c-malecki/power_supply_v2/Core/Src/adc.c

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
/* Includes ------------------------------------------------------------------*/
#include "adc.h"

ADC_HandleTypeDef hadc1;
ADC_HandleTypeDef hadc2;
ADC_HandleTypeDef hadc5;
DMA_HandleTypeDef hdma_adc1;
DMA_HandleTypeDef hdma_adc2;
DMA_HandleTypeDef hdma_adc5;

/* ADC1 init function */
void MX_ADC1_Init(void)
{

  ADC_MultiModeTypeDef multimode = {0};
  ADC_ChannelConfTypeDef sConfig = {0};

  /** Common config
  */
  hadc1.Instance = ADC1;
  hadc1.Init.ClockPrescaler = ADC_CLOCK_SYNC_PCLK_DIV4;
  hadc1.Init.Resolution = ADC_RESOLUTION_12B;
  hadc1.Init.DataAlign = ADC_DATAALIGN_RIGHT;
  hadc1.Init.GainCompensation = 0;
  hadc1.Init.ScanConvMode = ADC_SCAN_DISABLE;
  hadc1.Init.EOCSelection = ADC_EOC_SINGLE_CONV;
  hadc1.Init.LowPowerAutoWait = DISABLE;
  hadc1.Init.ContinuousConvMode = DISABLE;
  hadc1.Init.NbrOfConversion = 1;
  hadc1.Init.DiscontinuousConvMode = DISABLE;
  hadc1.Init.ExternalTrigConv = ADC_SOFTWARE_START;
  hadc1.Init.ExternalTrigConvEdge = ADC_EXTERNALTRIGCONVEDGE_NONE;
  hadc1.Init.DMAContinuousRequests = DISABLE;
  hadc1.Init.Overrun = ADC_OVR_DATA_PRESERVED;
  hadc1.Init.OversamplingMode = ENABLE;
  hadc1.Init.Oversampling.Ratio = ADC_OVERSAMPLING_RATIO_16;
  hadc1.Init.Oversampling.RightBitShift = ADC_RIGHTBITSHIFT_NONE;
  hadc1.Init.Oversampling.TriggeredMode = ADC_TRIGGEREDMODE_SINGLE_TRIGGER;
  hadc1.Init.Oversampling.OversamplingStopReset = ADC_REGOVERSAMPLING_CONTINUED_MODE;
  if (HAL_ADC_Init(&hadc1) != HAL_OK)
  {
    Error_Handler();
  }

  /** Configure the ADC multi-mode
  */
  multimode.Mode = ADC_MODE_INDEPENDENT;
  if (HAL_ADCEx_MultiModeConfigChannel(&hadc1, &multimode) != HAL_OK)
  {
    Error_Handler();
  }

  /** Configure Regular Channel
  */
  sConfig.Channel = ADC_CHANNEL_11;
  sConfig.Rank = ADC_REGULAR_RANK_1;
  sConfig.SamplingTime = ADC_SAMPLETIME_2CYCLES_5;
  sConfig.SingleDiff = ADC_SINGLE_ENDED;
  sConfig.OffsetNumber = ADC_OFFSET_NONE;
  sConfig.Offset = 0;
  if (HAL_ADC_ConfigChannel(&hadc1, &sConfig) != HAL_OK)
  {
    Error_Handler();
  }
}
/* ADC2 init function */
void MX_ADC2_Init(void)
{

  ADC_ChannelConfTypeDef sConfig = {0};

  /** Common config
  */
  hadc2.Instance = ADC2;
  hadc2.Init.ClockPrescaler = ADC_CLOCK_SYNC_PCLK_DIV4;
  hadc2.Init.Resolution = ADC_RESOLUTION_12B;
  hadc2.Init.DataAlign = ADC_DATAALIGN_RIGHT;
  hadc2.Init.GainCompensation = 0;
  hadc2.Init.ScanConvMode = ADC_SCAN_DISABLE;
  hadc2.Init.EOCSelection = ADC_EOC_SINGLE_CONV;
  hadc2.Init.LowPowerAutoWait = DISABLE;
  hadc2.Init.ContinuousConvMode = DISABLE;
  hadc2.Init.NbrOfConversion = 1;
  hadc2.Init.DiscontinuousConvMode = DISABLE;
  hadc2.Init.ExternalTrigConv = ADC_SOFTWARE_START;
  hadc2.Init.ExternalTrigConvEdge = ADC_EXTERNALTRIGCONVEDGE_NONE;
  hadc2.Init.DMAContinuousRequests = DISABLE;
  hadc2.Init.Overrun = ADC_OVR_DATA_PRESERVED;
  hadc2.Init.OversamplingMode = ENABLE;
  hadc2.Init.Oversampling.Ratio = ADC_OVERSAMPLING_RATIO_16;
  hadc2.Init.Oversampling.RightBitShift = ADC_RIGHTBITSHIFT_NONE;
  hadc2.Init.Oversampling.TriggeredMode = ADC_TRIGGEREDMODE_SINGLE_TRIGGER;
  hadc2.Init.Oversampling.OversamplingStopReset = ADC_REGOVERSAMPLING_CONTINUED_MODE;
  if (HAL_ADC_Init(&hadc2) != HAL_OK)
  {
    Error_Handler();
  }

  /** Configure Regular Channel
  */
  sConfig.Channel = ADC_CHANNEL_12;
  sConfig.Rank = ADC_REGULAR_RANK_1;
  sConfig.SamplingTime = ADC_SAMPLETIME_2CYCLES_5;
  sConfig.SingleDiff = ADC_SINGLE_ENDED;
  sConfig.OffsetNumber = ADC_OFFSET_NONE;
  sConfig.Offset = 0;
  if (HAL_ADC_ConfigChannel(&hadc2, &sConfig) != HAL_OK)
  {
    Error_Handler();
  }
}
/* ADC5 init function */
void MX_ADC5_Init(void)
{

  ADC_ChannelConfTypeDef sConfig = {0};

  /** Common config
  */
  hadc5.Instance = ADC5;
  hadc5.Init.ClockPrescaler = ADC_CLOCK_SYNC_PCLK_DIV4;
  hadc5.Init.Resolution = ADC_RESOLUTION_12B;
  hadc5.Init.DataAlign = ADC_DATAALIGN_RIGHT;
  hadc5.Init.GainCompensation = 0;
  hadc5.Init.ScanConvMode = ADC_SCAN_DISABLE;
  hadc5.Init.EOCSelection = ADC_EOC_SINGLE_CONV;
  hadc5.Init.LowPowerAutoWait = DISABLE;
  hadc5.Init.ContinuousConvMode = DISABLE;
  hadc5.Init.NbrOfConversion = 1;
  hadc5.Init.DiscontinuousConvMode = DISABLE;
  hadc5.Init.ExternalTrigConv = ADC_SOFTWARE_START;
  hadc5.Init.ExternalTrigConvEdge = ADC_EXTERNALTRIGCONVEDGE_NONE;
  hadc5.Init.DMAContinuousRequests = DISABLE;
  hadc5.Init.Overrun = ADC_OVR_DATA_PRESERVED;
  hadc5.Init.OversamplingMode = ENABLE;
  hadc5.Init.Oversampling.Ratio = ADC_OVERSAMPLING_RATIO_16;
  hadc5.Init.Oversampling.RightBitShift = ADC_RIGHTBITSHIFT_NONE;
  hadc5.Init.Oversampling.TriggeredMode = ADC_TRIGGEREDMODE_SINGLE_TRIGGER;
  hadc5.Init.Oversampling.OversamplingStopReset = ADC_REGOVERSAMPLING_CONTINUED_MODE;
  if (HAL_ADC_Init(&hadc5) != HAL_OK)
  {
    Error_Handler();
  }

  /** Configure Regular Channel
  */
  sConfig.Channel = ADC_CHANNEL_1;
  sConfig.Rank = ADC_REGULAR_RANK_1;
  sConfig.SamplingTime = ADC_SAMPLETIME_2CYCLES_5;
  sConfig.SingleDiff = ADC_SINGLE_ENDED;
  sConfig.OffsetNumber = ADC_OFFSET_NONE;
  sConfig.Offset = 0;
  if (HAL_ADC_ConfigChannel(&hadc5, &sConfig) != HAL_OK)
  {
    Error_Handler();
  }
}

static uint32_t HAL_RCC_ADC12_CLK_ENABLED=0;

void HAL_ADC_MspInit(ADC_HandleTypeDef* adcHandle)
{

  GPIO_InitTypeDef GPIO_InitStruct = {0};
  RCC_PeriphCLKInitTypeDef PeriphClkInit = {0};
  if(adcHandle->Instance==ADC1)
  {
  /** Initializes the peripherals clocks
  */
    PeriphClkInit.PeriphClockSelection = RCC_PERIPHCLK_ADC12;
    PeriphClkInit.Adc12ClockSelection = RCC_ADC12CLKSOURCE_SYSCLK;
    if (HAL_RCCEx_PeriphCLKConfig(&PeriphClkInit) != HAL_OK)
    {
      Error_Handler();
    }

    /* ADC1 clock enable */
    HAL_RCC_ADC12_CLK_ENABLED++;
    if(HAL_RCC_ADC12_CLK_ENABLED==1){
      __HAL_RCC_ADC12_CLK_ENABLE();
    }

    __HAL_RCC_GPIOB_CLK_ENABLE();
    /**ADC1 GPIO Configuration
    PB11     ------> ADC1_IN14
    PB12     ------> ADC1_IN11
    */
    GPIO_InitStruct.Pin = OPAMP_3V3B_ADC1_IN14_Pin|OPAMP_3V3A_ADC1_IN11_Pin;
    GPIO_InitStruct.Mode = GPIO_MODE_ANALOG;
    GPIO_InitStruct.Pull = GPIO_NOPULL;
    HAL_GPIO_Init(GPIOB, &GPIO_InitStruct);

    /* ADC1 DMA Init */
    /* ADC1 Init */
    hdma_adc1.Instance = DMA1_Channel3;
    hdma_adc1.Init.Request = DMA_REQUEST_ADC1;
    hdma_adc1.Init.Direction = DMA_PERIPH_TO_MEMORY;
    hdma_adc1.Init.PeriphInc = DMA_PINC_DISABLE;
    hdma_adc1.Init.MemInc = DMA_MINC_ENABLE;
    hdma_adc1.Init.PeriphDataAlignment = DMA_PDATAALIGN_HALFWORD;
    hdma_adc1.Init.MemDataAlignment = DMA_MDATAALIGN_HALFWORD;
    hdma_adc1.Init.Mode = DMA_CIRCULAR;
    hdma_adc1.Init.Priority = DMA_PRIORITY_LOW;
    if (HAL_DMA_Init(&hdma_adc1) != HAL_OK)
    {
      Error_Handler();
    }

    __HAL_LINKDMA(adcHandle,DMA_Handle,hdma_adc1);

    /* ADC1 interrupt Init */
    HAL_NVIC_SetPriority(ADC1_2_IRQn, 0, 0);
    HAL_NVIC_EnableIRQ(ADC1_2_IRQn);
  }
  else if(adcHandle->Instance==ADC2)
  {
  /** Initializes the peripherals clocks
  */
    PeriphClkInit.PeriphClockSelection = RCC_PERIPHCLK_ADC12;
    PeriphClkInit.Adc12ClockSelection = RCC_ADC12CLKSOURCE_SYSCLK;
    if (HAL_RCCEx_PeriphCLKConfig(&PeriphClkInit) != HAL_OK)
    {
      Error_Handler();
    }

    /* ADC2 clock enable */
    HAL_RCC_ADC12_CLK_ENABLED++;
    if(HAL_RCC_ADC12_CLK_ENABLED==1){
      __HAL_RCC_ADC12_CLK_ENABLE();
    }

    __HAL_RCC_GPIOB_CLK_ENABLE();
    /**ADC2 GPIO Configuration
    PB2     ------> ADC2_IN12
    */
    GPIO_InitStruct.Pin = INA_5VB_ADC2_IN12_Pin;
    GPIO_InitStruct.Mode = GPIO_MODE_ANALOG;
    GPIO_InitStruct.Pull = GPIO_NOPULL;
    HAL_GPIO_Init(INA_5VB_ADC2_IN12_GPIO_Port, &GPIO_InitStruct);

    /* ADC2 DMA Init */
    /* ADC2 Init */
    hdma_adc2.Instance = DMA1_Channel2;
    hdma_adc2.Init.Request = DMA_REQUEST_ADC2;
    hdma_adc2.Init.Direction = DMA_PERIPH_TO_MEMORY;
    hdma_adc2.Init.PeriphInc = DMA_PINC_DISABLE;
    hdma_adc2.Init.MemInc = DMA_MINC_ENABLE;
    hdma_adc2.Init.PeriphDataAlignment = DMA_PDATAALIGN_HALFWORD;
    hdma_adc2.Init.MemDataAlignment = DMA_MDATAALIGN_HALFWORD;
    hdma_adc2.Init.Mode = DMA_CIRCULAR;
    hdma_adc2.Init.Priority = DMA_PRIORITY_LOW;
    if (HAL_DMA_Init(&hdma_adc2) != HAL_OK)
    {
      Error_Handler();
    }

    __HAL_LINKDMA(adcHandle,DMA_Handle,hdma_adc2);

    /* ADC2 interrupt Init */
    HAL_NVIC_SetPriority(ADC1_2_IRQn, 0, 0);
    HAL_NVIC_EnableIRQ(ADC1_2_IRQn);
  }
  else if(adcHandle->Instance==ADC5)
  {
  /** Initializes the peripherals clocks
  */
    PeriphClkInit.PeriphClockSelection = RCC_PERIPHCLK_ADC345;
    PeriphClkInit.Adc345ClockSelection = RCC_ADC345CLKSOURCE_SYSCLK;
    if (HAL_RCCEx_PeriphCLKConfig(&PeriphClkInit) != HAL_OK)
    {
      Error_Handler();
    }

    /* ADC5 clock enable */
    __HAL_RCC_ADC345_CLK_ENABLE();

    __HAL_RCC_GPIOA_CLK_ENABLE();
    /**ADC5 GPIO Configuration
    PA8     ------> ADC5_IN1
    PA9     ------> ADC5_IN2
    */
    GPIO_InitStruct.Pin = INA_VVAR_ADC5_IN1_Pin|INA_20V_ADC5_IN2_Pin;
    GPIO_InitStruct.Mode = GPIO_MODE_ANALOG;
    GPIO_InitStruct.Pull = GPIO_NOPULL;
    HAL_GPIO_Init(GPIOA, &GPIO_InitStruct);

    /* ADC5 DMA Init */
    /* ADC5 Init */
    hdma_adc5.Instance = DMA1_Channel1;
    hdma_adc5.Init.Request = DMA_REQUEST_ADC5;
    hdma_adc5.Init.Direction = DMA_PERIPH_TO_MEMORY;
    hdma_adc5.Init.PeriphInc = DMA_PINC_DISABLE;
    hdma_adc5.Init.MemInc = DMA_MINC_ENABLE;
    hdma_adc5.Init.PeriphDataAlignment = DMA_PDATAALIGN_HALFWORD;
    hdma_adc5.Init.MemDataAlignment = DMA_MDATAALIGN_HALFWORD;
    hdma_adc5.Init.Mode = DMA_CIRCULAR;
    hdma_adc5.Init.Priority = DMA_PRIORITY_LOW;
    if (HAL_DMA_Init(&hdma_adc5) != HAL_OK)
    {
      Error_Handler();
    }

    __HAL_LINKDMA(adcHandle,DMA_Handle,hdma_adc5);

    /* ADC5 interrupt Init */
    HAL_NVIC_SetPriority(ADC5_IRQn, 0, 0);
    HAL_NVIC_EnableIRQ(ADC5_IRQn);
  }
}

void HAL_ADC_MspDeInit(ADC_HandleTypeDef* adcHandle)
{

  if(adcHandle->Instance==ADC1)
  {
    /* Peripheral clock disable */
    HAL_RCC_ADC12_CLK_ENABLED--;
    if(HAL_RCC_ADC12_CLK_ENABLED==0){
      __HAL_RCC_ADC12_CLK_DISABLE();
    }

    /**ADC1 GPIO Configuration
    PB11     ------> ADC1_IN14
    PB12     ------> ADC1_IN11
    */
    HAL_GPIO_DeInit(GPIOB, OPAMP_3V3B_ADC1_IN14_Pin|OPAMP_3V3A_ADC1_IN11_Pin);

    /* ADC1 DMA DeInit */
    HAL_DMA_DeInit(adcHandle->DMA_Handle);

    /* ADC1 interrupt Deinit */
  /* USER CODE BEGIN ADC1:ADC1_2_IRQn disable */
    /**
    * Uncomment the line below to disable the "ADC1_2_IRQn" interrupt
    * Be aware, disabling shared interrupt may affect other IPs
    */
    /* HAL_NVIC_DisableIRQ(ADC1_2_IRQn); */
  /* USER CODE END ADC1:ADC1_2_IRQn disable */

  }
  else if(adcHandle->Instance==ADC2)
  {
    /* Peripheral clock disable */
    HAL_RCC_ADC12_CLK_ENABLED--;
    if(HAL_RCC_ADC12_CLK_ENABLED==0){
      __HAL_RCC_ADC12_CLK_DISABLE();
    }

    /**ADC2 GPIO Configuration
    PB2     ------> ADC2_IN12
    */
    HAL_GPIO_DeInit(INA_5VB_ADC2_IN12_GPIO_Port, INA_5VB_ADC2_IN12_Pin);

    /* ADC2 DMA DeInit */
    HAL_DMA_DeInit(adcHandle->DMA_Handle);

    /* ADC2 interrupt Deinit */
  /* USER CODE BEGIN ADC2:ADC1_2_IRQn disable */
    /**
    * Uncomment the line below to disable the "ADC1_2_IRQn" interrupt
    * Be aware, disabling shared interrupt may affect other IPs
    */
    /* HAL_NVIC_DisableIRQ(ADC1_2_IRQn); */
  /* USER CODE END ADC2:ADC1_2_IRQn disable */

  }
  else if(adcHandle->Instance==ADC5)
  {
    /* Peripheral clock disable */
    __HAL_RCC_ADC345_CLK_DISABLE();

    /**ADC5 GPIO Configuration
    PA8     ------> ADC5_IN1
    PA9     ------> ADC5_IN2
    */
    HAL_GPIO_DeInit(GPIOA, INA_VVAR_ADC5_IN1_Pin|INA_20V_ADC5_IN2_Pin);

    /* ADC5 DMA DeInit */
    HAL_DMA_DeInit(adcHandle->DMA_Handle);

    /* ADC5 interrupt Deinit */
    HAL_NVIC_DisableIRQ(ADC5_IRQn);
  }
}
