c-malecki/power_supply_v2/App/controllers/power.c

#include <stdbool.h>
#include <stdint.h>
#include <stdio.h>

#include "gpio.h"
#include "main.h"
#include "stm32g474xx.h"
#include "stm32g4xx_hal.h"
#include "stm32g4xx_hal_def.h"

#include "common.h"
#include "power.h"

void Pwr_Chan_SetVarV(Pwr_Ctrl_t *ctrl, int32_t target_voltage_w, uint32_t target_voltage_d);
void Power_Controller_UpdateVarValues(Pwr_Ctrl_t *ctrl);

static const Pwr_Chan_t channel_3v3_default = {
    .toggle_pending = false,
    .output_on = false,
    .sw_pin = HSSW_3V3B_Pin,
    .sw_port = HSSW_3V3B_GPIO_Port,
};

static const Pwr_Chan_t channel_5v_default = {
    .toggle_pending = false,
    .output_on = false,
    .sw_pin = HSSW_5VB_Pin,
    .sw_port = HSSW_5VB_GPIO_Port,
};

static const Pwr_Chan_t channel_var_default = {
    .toggle_pending = false,
    .output_on = false,
    .sw_pin = BUCK_VVAR_EN_Pin,
    .sw_port = BUCK_VVAR_EN_GPIO_Port,
};

static const Pwr_Var_Control_t var_ctrls_default = {
    .pid_p_gain = 0.0f,
    .pid_i_gain = 0.0f,
    .pid_acc_error = 0.0f,
    .pid_prev_error = 0.0f,
    .target_voltage_w = VOLTAGE_VARIABLE_MIN_WHOLE,
    .target_voltage_d = VOLTAGE_VARIABLE_MIN_DECIMAL,
    .pid_last_time = 0,
};

static const Pwr_Buck_t buck_5v_default = {
    .power_on = false,
    .gpio_pin = BUCK_5V_EN_Pin,
    .gpio_port = BUCK_5V_EN_GPIO_Port,
};

static const Pwr_Buck_t buck_12v_default = {
    .power_on = false,
    .gpio_pin = BUCK_12V_EN_Pin,
    .gpio_port = BUCK_12V_EN_GPIO_Port,
};

static const Pwr_Buck_t buck_vvar_default = {
    .power_on = false,
    .gpio_pin = BUCK_VVAR_EN_Pin,
    .gpio_port = BUCK_VVAR_EN_GPIO_Port,
};

void Pwr_Ctrl_Init(Pwr_Ctrl_t *ctrl)
{
    ctrl->channels[PWR_CHAN_3V3] = channel_3v3_default;
    ctrl->channels[PWR_CHAN_5V] = channel_5v_default;
    ctrl->channels[PWR_CHAN_VVAR] = channel_var_default;
    ctrl->bucks[PWR_BUCK_5V] = buck_5v_default;
    ctrl->bucks[PWR_BUCK_12V] = buck_12v_default;
    ctrl->bucks[PWR_BUCK_VVAR] = buck_vvar_default;
    ctrl->var_ctrls = var_ctrls_default;
}

void Pwr_Buck_Toggle(Pwr_Ctrl_t *ctrl, Pwr_Buck buck)
{
    Pwr_Buck_t *b = &ctrl->bucks[buck];
    bool new_state = !b->power_on;
    HAL_GPIO_WritePin(b->gpio_port, b->gpio_pin, new_state);
    b->power_on = new_state;
}

void Pwr_Chan_Toggle(Pwr_Ctrl_t *ctrl, Pwr_Chan channel)
{
    Pwr_Chan_t *chan = &ctrl->channels[channel];
    uint8_t new_state = !chan->output_on;

    HAL_GPIO_WritePin(chan->sw_port, chan->sw_pin, new_state);

    if (channel == PWR_CHAN_VVAR) {
        ctrl->var_ctrls.pid_p_gain = 50.0f;
        ctrl->var_ctrls.pid_i_gain = 5.0f;
        ctrl->var_ctrls.pid_acc_error = 0.0f;
        ctrl->var_ctrls.pid_prev_error = 0.0f;
        ctrl->var_ctrls.pid_last_time = HAL_GetTick();
        // TODO: start pid
        if (!chan->output_on) {
            Pwr_Chan_SetVarV(ctrl, VOLTAGE_VARIABLE_MIN_WHOLE, VOLTAGE_VARIABLE_MIN_DECIMAL);
        } else {
            Pwr_Chan_SetVarV(ctrl, ctrl->var_ctrls.target_voltage_w,
                             ctrl->var_ctrls.target_voltage_d);
        }
    }

    chan->toggle_pending = false;
    chan->output_on = new_state;
}

void Pwr_Chan_SetVarV(Pwr_Ctrl_t *ctrl, int32_t target_voltage_w, uint32_t target_voltage_d)
{
    // if (target_voltage_w < VOLTAGE_VARIABLE_MIN_WHOLE) {
    //     target_voltage_w = VOLTAGE_VARIABLE_MIN_WHOLE;
    //     target_voltage_d = 0;
    // }

    // if (target_voltage_w > VOLTAGE_VARIABLE_MAX_WHOLE) {
    //     target_voltage_w = VOLTAGE_VARIABLE_MAX_WHOLE;
    //     target_voltage_d = 0;
    // }

    // _Error_Codes code = MCP_VoltageToSteps(&ctrl->var_ctrls.mcp, ctrl->i2c_handle,
    // target_voltage_w,
    //                                        target_voltage_d);
    // if (code != ERROR_NONE) {
    //     ctrl->error_cb(ctrl->error_ctx,
    //                    (_Error_t) { .controller = CONTROLLER_POWER,
    //                                 .peripheral = PERIPHERAL_MCP,
    //                                 .code = code,
    //                                 .function = FUNCTION_MCP_V_TO_S });
    // }

    // ctrl->var_ctrls.target_voltage_w = target_voltage_w;
    // ctrl->var_ctrls.target_voltage_d = target_voltage_d;
}

// void Pwr_Ctrl_Ping(Pwr_Ctrl_t *ctrl)
// {
//     _Error_Codes code;
//     for (uint8_t i = 0; i < PWR_BUCK_COUNT; i++) {
//         Pwr_Buck_t buck = ctrl->bucks[i];

//         code = ConvHALError(HAL_I2C_IsDeviceReady(ctrl->i2c_handle, buck.ina.i2c_addr, 3, 100));
//         if (code != ERROR_NONE) {
//             ctrl->error_cb(ctrl->error_ctx,
//                            (_Error_t) { .controller = CONTROLLER_POWER,
//                                         .peripheral = PERIPHERAL_INA_MAIN,
//                                         .code = code,
//                                         .function = FUNCTION_INA_PING });
//         }
//     }

//     code = ConvHALError(HAL_I2C_IsDeviceReady(ctrl->i2c_handle, MCP_I2C_ADDR, 3, 100));
//     if (code != ERROR_NONE) {
//         ctrl->error_cb(ctrl->error_ctx,
//                        (_Error_t) { .controller = CONTROLLER_POWER,
//                                     .peripheral = PERIPHERAL_MCP,
//                                     .code = code,
//                                     .function = FUNCTION_MCP_PING });
//     }
// }

// void Pwr_Ctrl_Run(Pwr_Ctrl_t *ctrl)
// {
//     _Error_Codes code;

//     for (uint8_t i = 0; i < PWR_BUCK_COUNT; i++) {
//         Pwr_Buck_t buck = ctrl->bucks[i];

//         code = INA_Init(&buck.ina, ctrl->i2c_handle);
//         if (code != ERROR_NONE) {
//             ctrl->error_cb(ctrl->error_ctx,
//                            (_Error_t) { .controller = CONTROLLER_POWER,
//                                         .peripheral = PERIPHERAL_INA_MAIN,
//                                         .code = code,
//                                         .function = FUNCTION_INA_INIT });
//         }
//     }
// }

// static uint8_t var_pi_start(Channel_VAR_t *chan, I2C_HandleTypeDef *i2c_handle);

/*
Your DAC is inverted (lower DAC = higher voltage). If error is positive (need more voltage), you
want to decrease DAC steps:

    int16_t adjustment = -(int16_t)step_adjustment;  // Negate for inverted

DAC Test this - if PI drives the wrong direction, add the negative sign.

Consider deadband to prevent oscillation:

    if (fabs(error) < 0.05f) {  // Within 50mV, don't adjust
        return ERROR_NONE;
    }
*/
// static uint8_t var_pi_start(Channel_VAR_t *chan, I2C_HandleTypeDef *i2c_handle)
// {
//     uint8_t err;
//     float error = chan->target_voltage - chan->cur_voltage;

//     uint32_t current_time = HAL_GetTick();
//     float delta_time = (current_time - chan->pid.pid_last_time) / 1000.0f;

//     if (delta_time > 1.0f) {
//         chan->pid.pid_last_time = current_time;
//         return ERROR_NONE;
//     }

//     chan->pid.pid_last_time = current_time;

//     float proportion = chan->pid.pid_p_gain * error;
//     chan->pid.acc_err += error * delta_time;

//     if (chan->pid.acc_err > 500.0f) {
//         chan->pid.acc_err = 500.0f;
//     }
//     if (chan->pid.acc_err < -500.0f) {
//         chan->pid.acc_err = -500.0f;
//     }

//     float integral = chan->pid.pid_i_gain * chan->pid.acc_err;
//     float step_adjustment = proportion + integral;

//     int16_t adjustment = (int16_t)step_adjustment;
//     int16_t dac_steps = (int16_t)chan->cur_dac_steps + adjustment;

//     if (dac_steps < 0) {
//         dac_steps = 0;
//     }
//     if (dac_steps > 3250) {
//         dac_steps = 3250;
//     }

//     err = MCP_VoltageToSteps(i2c_handle, (uint16_t)dac_steps);
//     if (err != ERROR_NONE) {
//         return err;
//     }

//     if (chan->cur_current > INA_CURRENT_TRESHOLD) {
//         Channel_VAR_EnableOutput(chan, false);
//         return 5;
//     }

//     return ERROR_NONE;
// }
