c-malecki/power_supply_v2/Tests/tests.h

#ifndef __TESTS_H__
#define __TESTS_H__

#include "app.h"

void Test_Display(App_t *app);
void Test_LEDs(App_t *app);
void Test_Power(App_t *app);
void Test_Temperature(App_t *app);
void Test_PrintAppState(App_t *app);

#endif // __TESTS_H__
